JiriS97/LithiumBMS/PCB/v1.0/PDF/LithiumBMS-B.SilkS.pdf

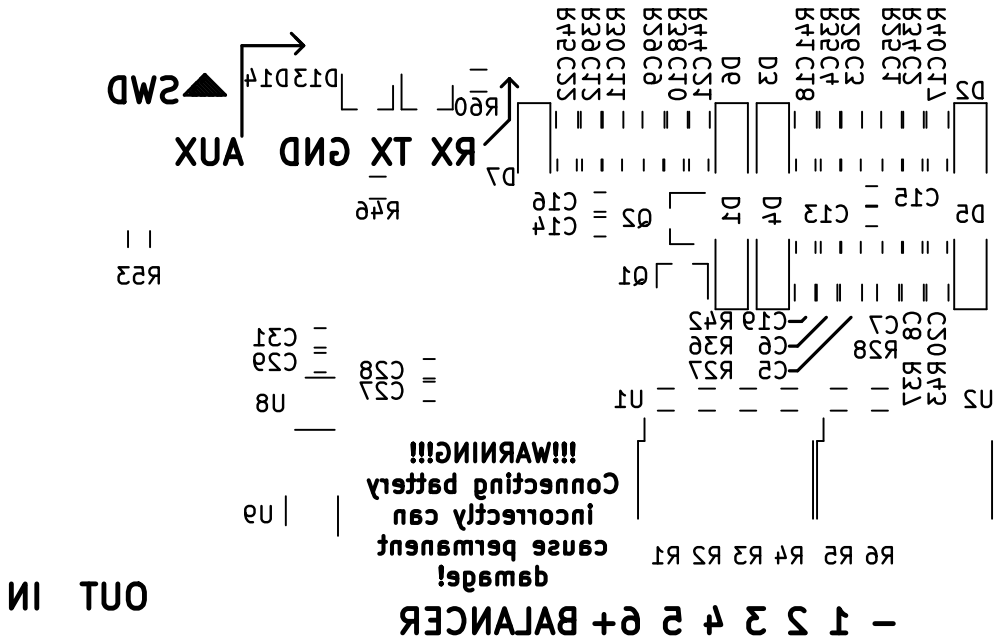
[picture p20: page 1]
