JiriS97/LithiumBMS/PCB/v1.0/PDF/LithiumBMS-F.Cu.pdf

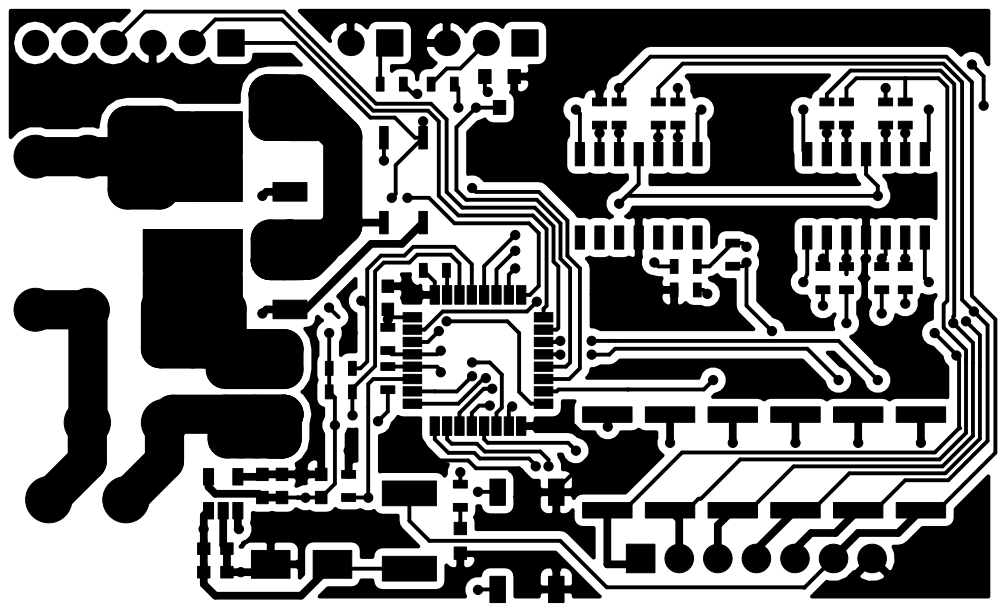
[picture p21: page 1]
