JiriS97/LithiumBMS/PCB/v1.0/PDF/LithiumBMS-F.Mask.pdf

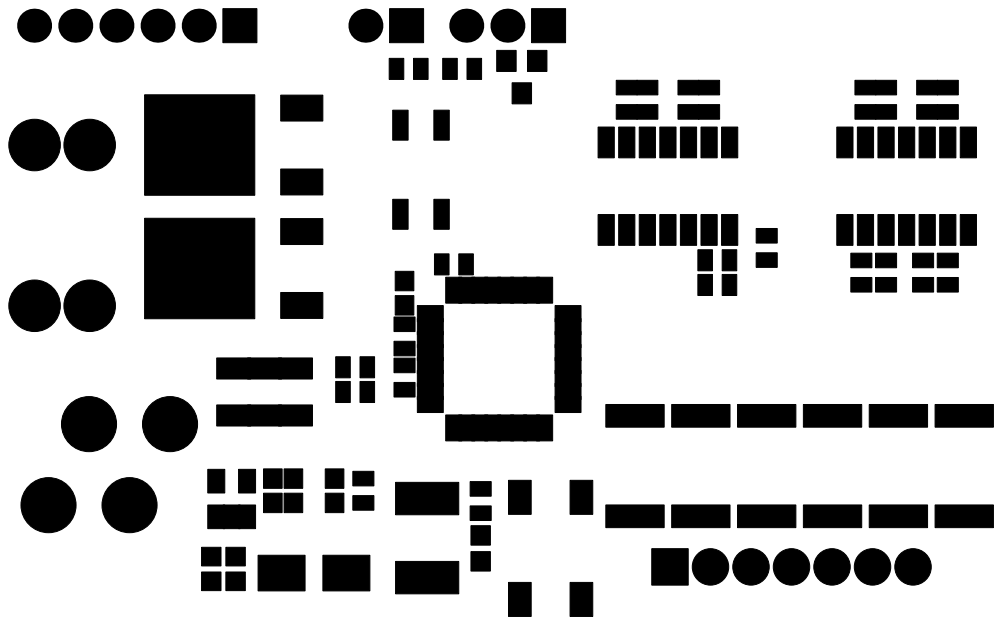
[picture p22: page 1]
