JiriS97/LithiumBMS/PCB/v1.0/PDF/LithiumBMS-F.SilkS.pdf

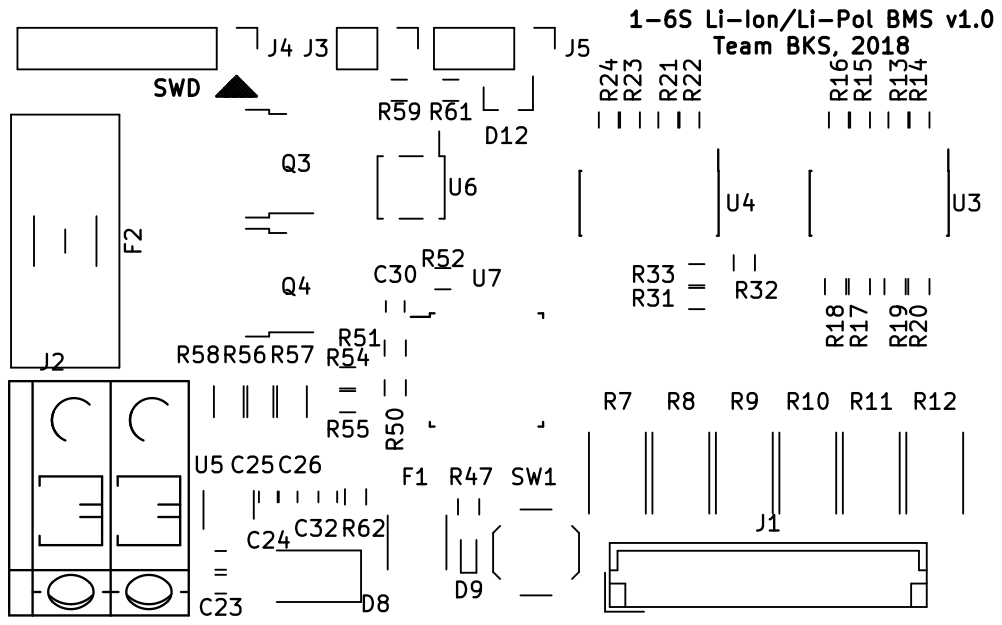
[picture p23: page 1]
