JiriS97/LithiumBMS/PCB/v1.0/PDF/LithiumBMS.pdf

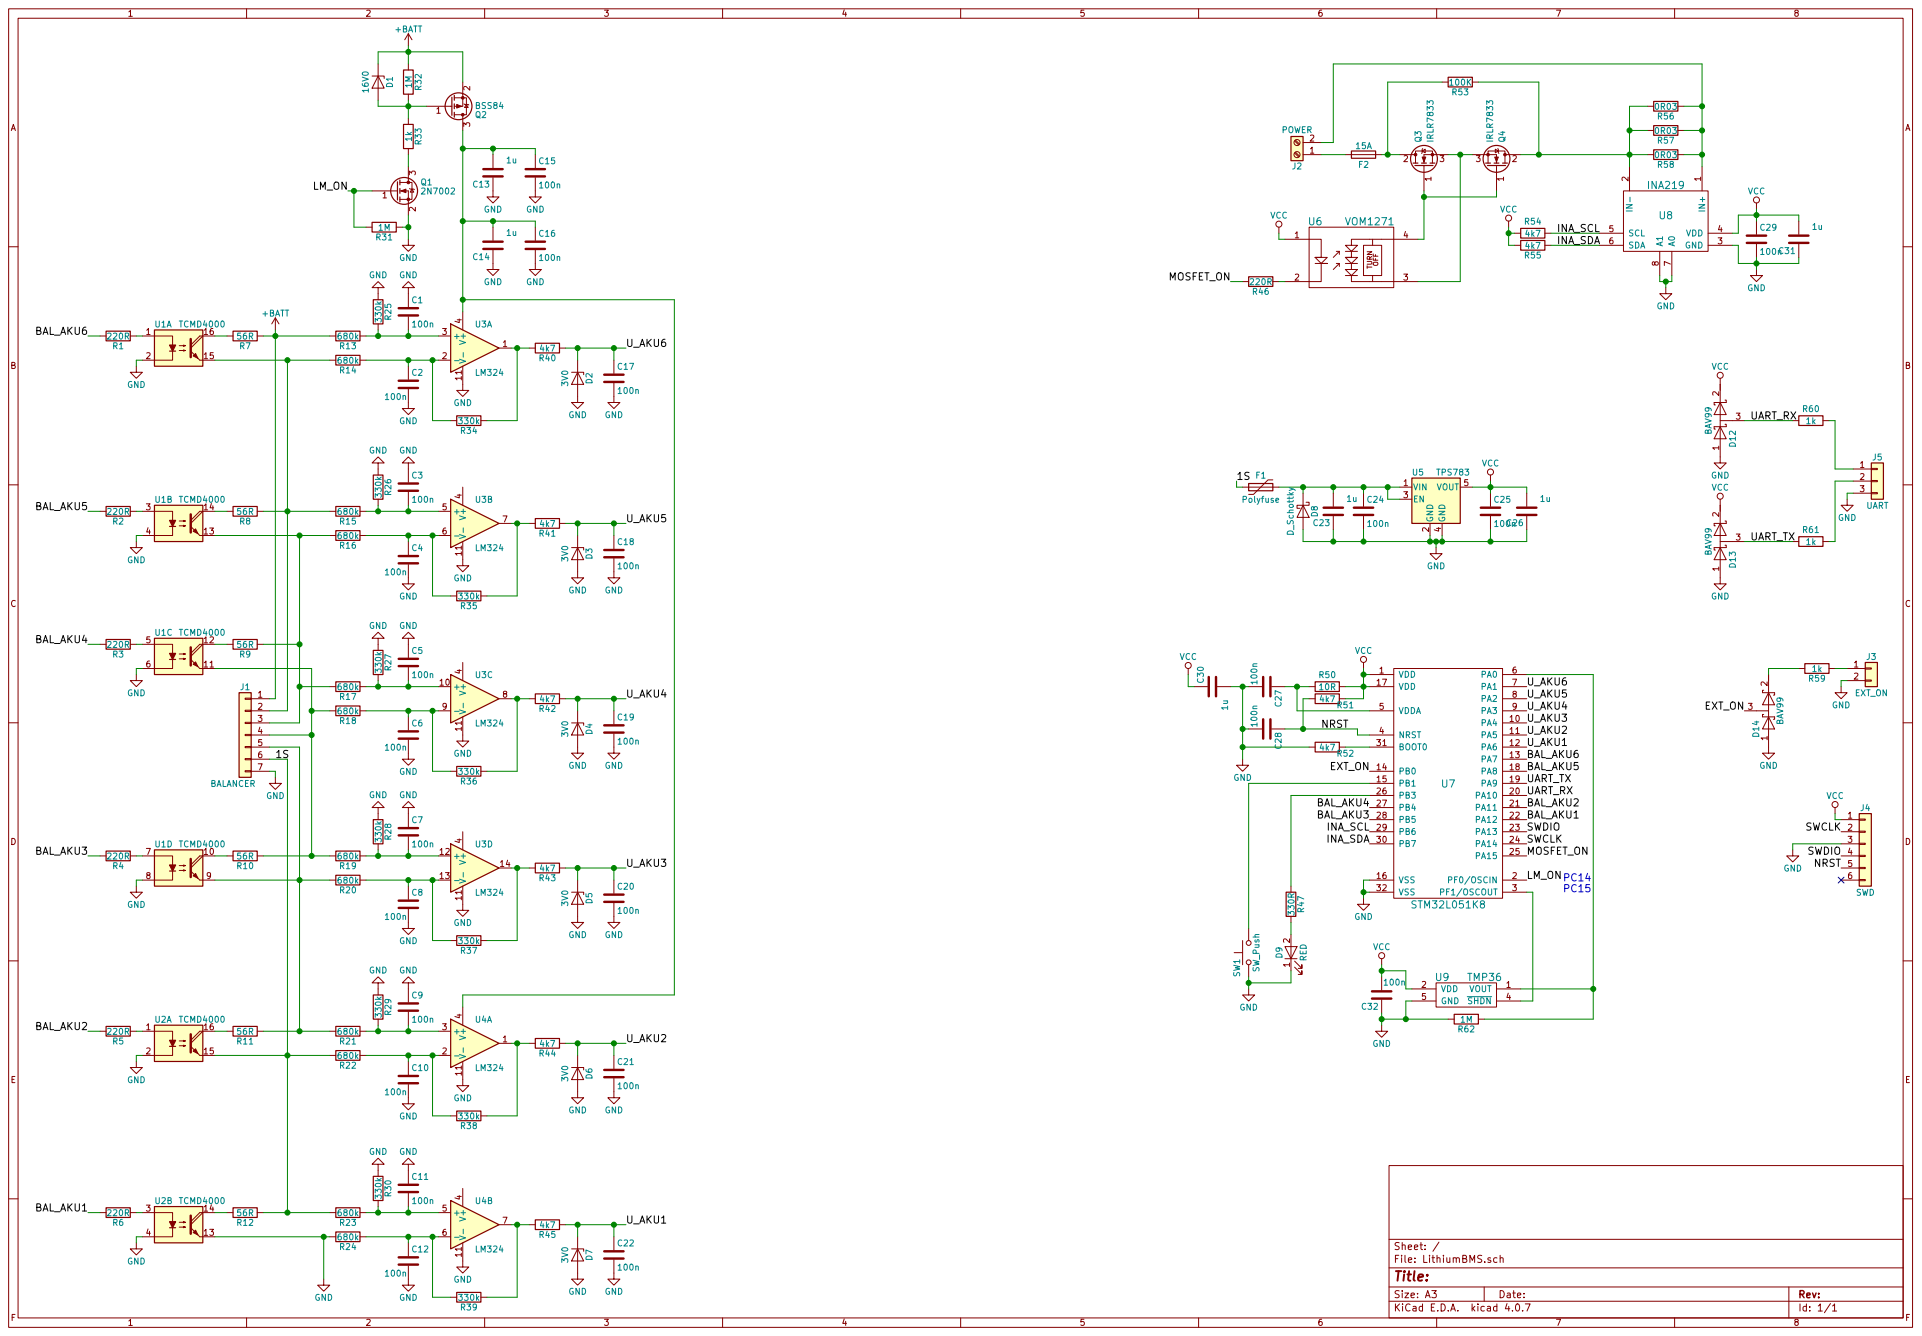
[picture p24: page 1]
